ARognes/Gravi/V0.1/Choc/main.kicad_sch

## KiCad design V0.1/Choc/main.kicad_sch (2022-05-29, an earlier design)

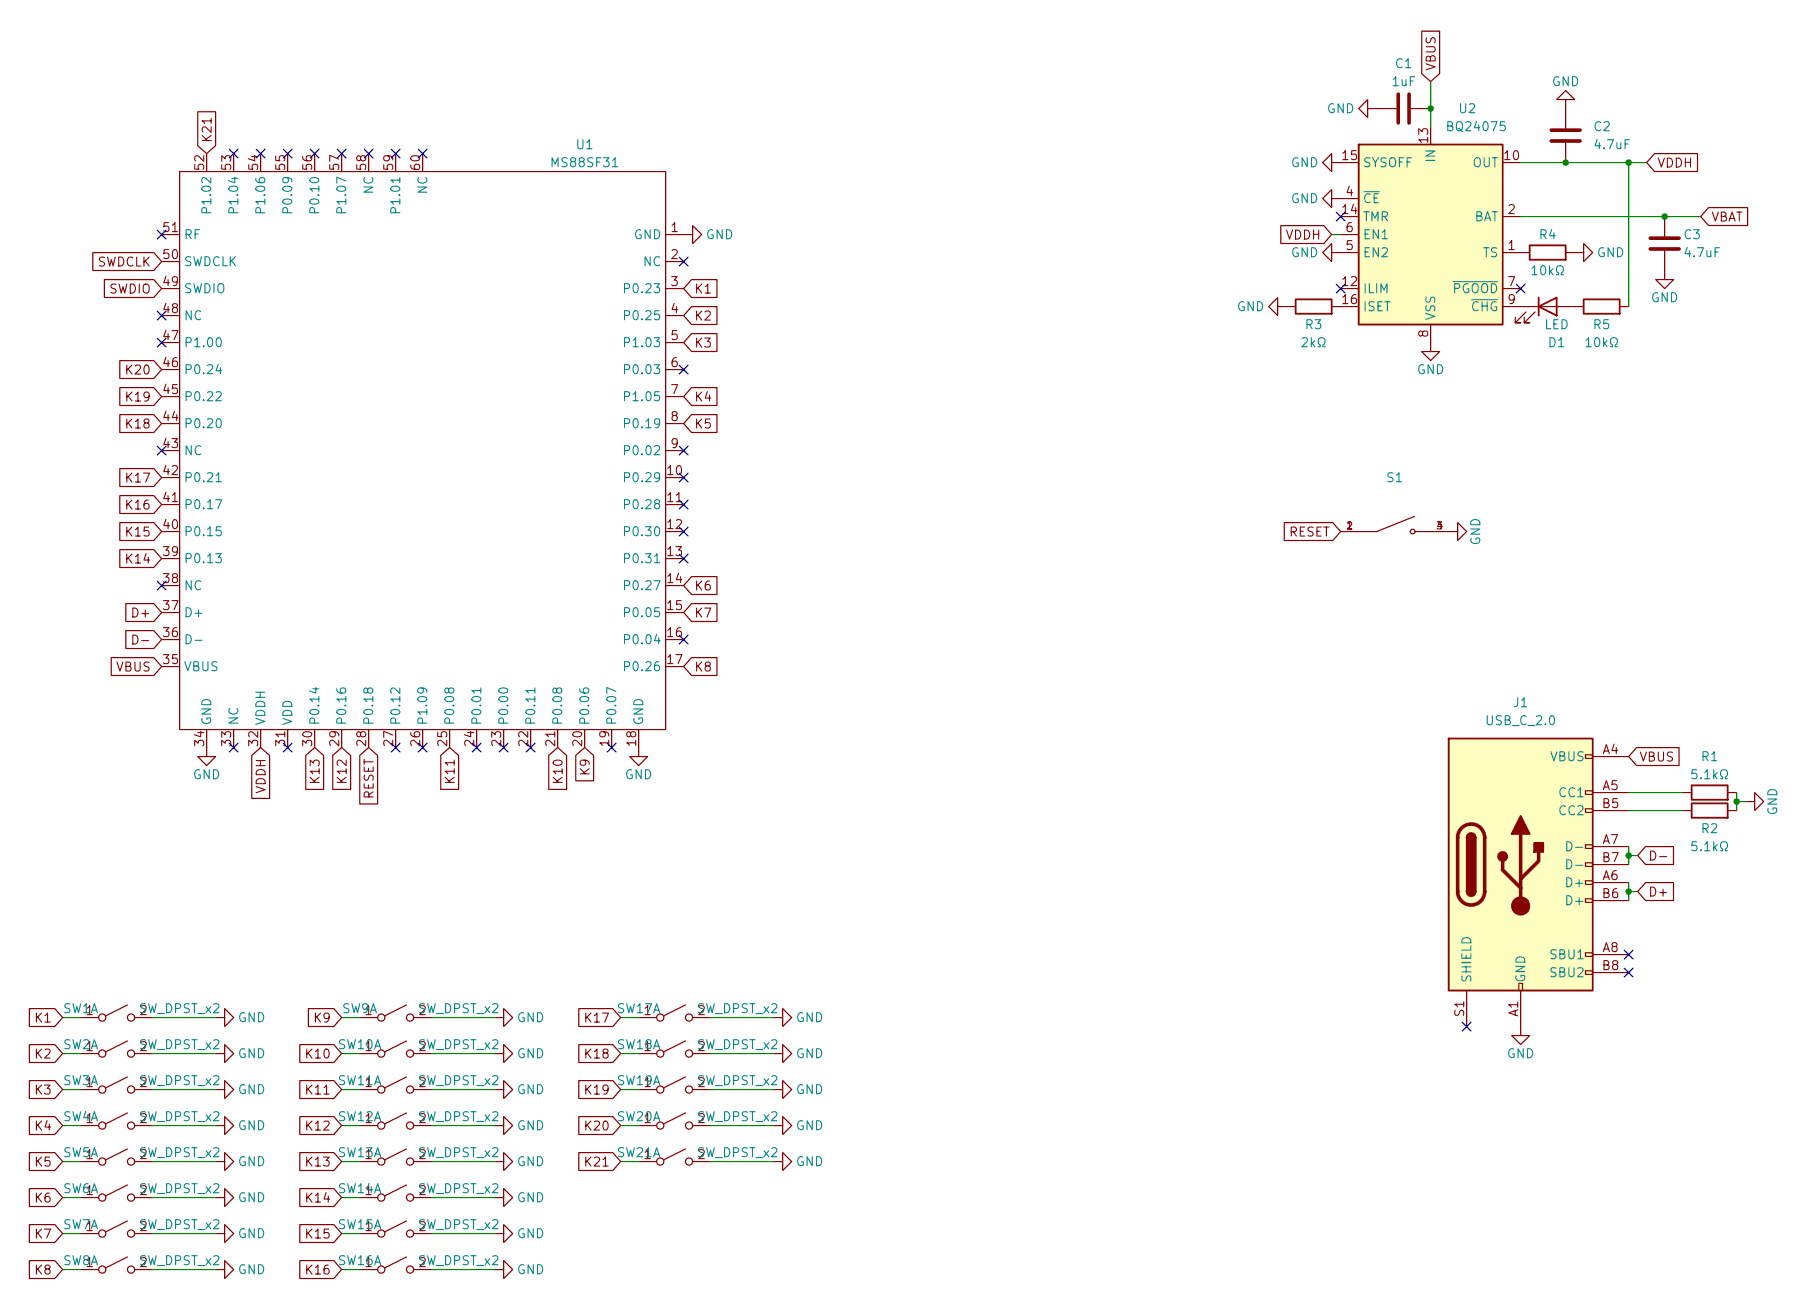
[picture p16: schematic main.kicad_sch]

Parts:
C1: 1uF
C2, C3: 4.7uF
D1: LED
J1: USB_C_2.0
R1, R2: 5.1kΩ
R3: 2kΩ
R4, R5: 10kΩ
S1: PARTREV 20 mar 19
SW1, SW2, SW3, SW4, SW5, SW6, SW7, SW8, SW9, SW10, SW11, SW12, SW13, SW14, SW15, SW16, SW17, SW18, SW19, SW20, SW21: SW_DPST_x2
U1: MS88SF31; MS88SF3
U2: BQ24075; VQFN-16-1EP_3x3mm_P0.5mm_EP1.6x1.6mm

Connections:
D+: J1.A6 (D+), J1.B6 (D+), U1.37 (D+)
D-: J1.A7 (D-), J1.B7 (D-), U1.36 (D-)
GND: C1.1, C2.2, C3.1, J1.A1 (GND), J1.A12 (GND), J1.B1 (GND), J1.B12 (GND), R1.2, R2.2, R3.1, R4.2, SW1.2 (B), SW2.2 (B), SW3.2 (B), SW4.2 (B), SW5.2 (B), SW6.2 (B), SW7.2 (B), SW8.2 (B), SW9.2 (B), SW10.2 (B), SW11.2 (B), SW12.2 (B), SW13.2 (B), SW14.2 (B), SW15.2 (B), SW16.2 (B), SW17.2 (B), SW18.2 (B), SW19.2 (B), SW20.2 (B), SW21.2 (B), U1.1 (GND), U1.18 (GND), U1.34 (GND), U2.4 (~CE), U2.5 (EN2), U2.8 (VSS), U2.15 (SYSOFF), U2.17 (VSS)
K1: SW1.1 (A), U1.3 (P0.23)
K2: SW2.1 (A), U1.4 (P0.25)
K3: SW3.1 (A), U1.5 (P1.03)
K4: SW4.1 (A), U1.7 (P1.05)
K5: SW5.1 (A), U1.8 (P0.19)
K6: SW6.1 (A), U1.14 (P0.27)
K7: SW7.1 (A), U1.15 (P0.05)
K8: SW8.1 (A), U1.17 (P0.26)
K9: SW9.1 (A), U1.20 (P0.06)
K10: SW10.1 (A), U1.21 (P0.08)
K11: SW11.1 (A), U1.25 (P0.08)
K12: SW12.1 (A), U1.29 (P0.16)
K13: SW13.1 (A), U1.30 (P0.14)
K14: SW14.1 (A), U1.39 (P0.13)
K15: SW15.1 (A), U1.40 (P0.15)
K16: SW16.1 (A), U1.41 (P0.17)
K17: SW17.1 (A), U1.42 (P0.21)
K18: SW18.1 (A), U1.44 (P0.20)
K19: SW19.1 (A), U1.45 (P0.22)
K20: SW20.1 (A), U1.46 (P0.24)
K21: SW21.1 (A), U1.52 (P1.02)
unnamed: D1.1 (K), U2.9 (~CHG)
unnamed: D1.2 (A), R5.1
unnamed: J1.A5 (CC1), R1.1
unnamed: J1.B5 (CC2), R2.1
unnamed: R3.2, U2.16 (ISET)
unnamed: R4.1, U2.1 (TS)
unnamed: S1.3, S1.4
RESET: S1.1, S1.2, U1.28 (P0.18)
SWDCLK: U1.50 (SWDCLK)
SWDIO: U1.49 (SWDIO)
VBAT: C3.2, U2.2 (BAT), U2.3 (BAT)
VBUS: C1.2, J1.A4 (VBUS), J1.A9 (VBUS), J1.B4 (VBUS), J1.B9 (VBUS), U1.35 (VBUS), U2.13 (IN)
VDDH: C2.1, R5.2, U1.32 (VDDH), U2.6 (EN1), U2.10 (OUT), U2.11 (OUT)
