ARognes/Gravi/V0.2/Choc/main.kicad_sch

## KiCad design V0.2/Choc/main.kicad_sch (2022-08-15, an earlier design)

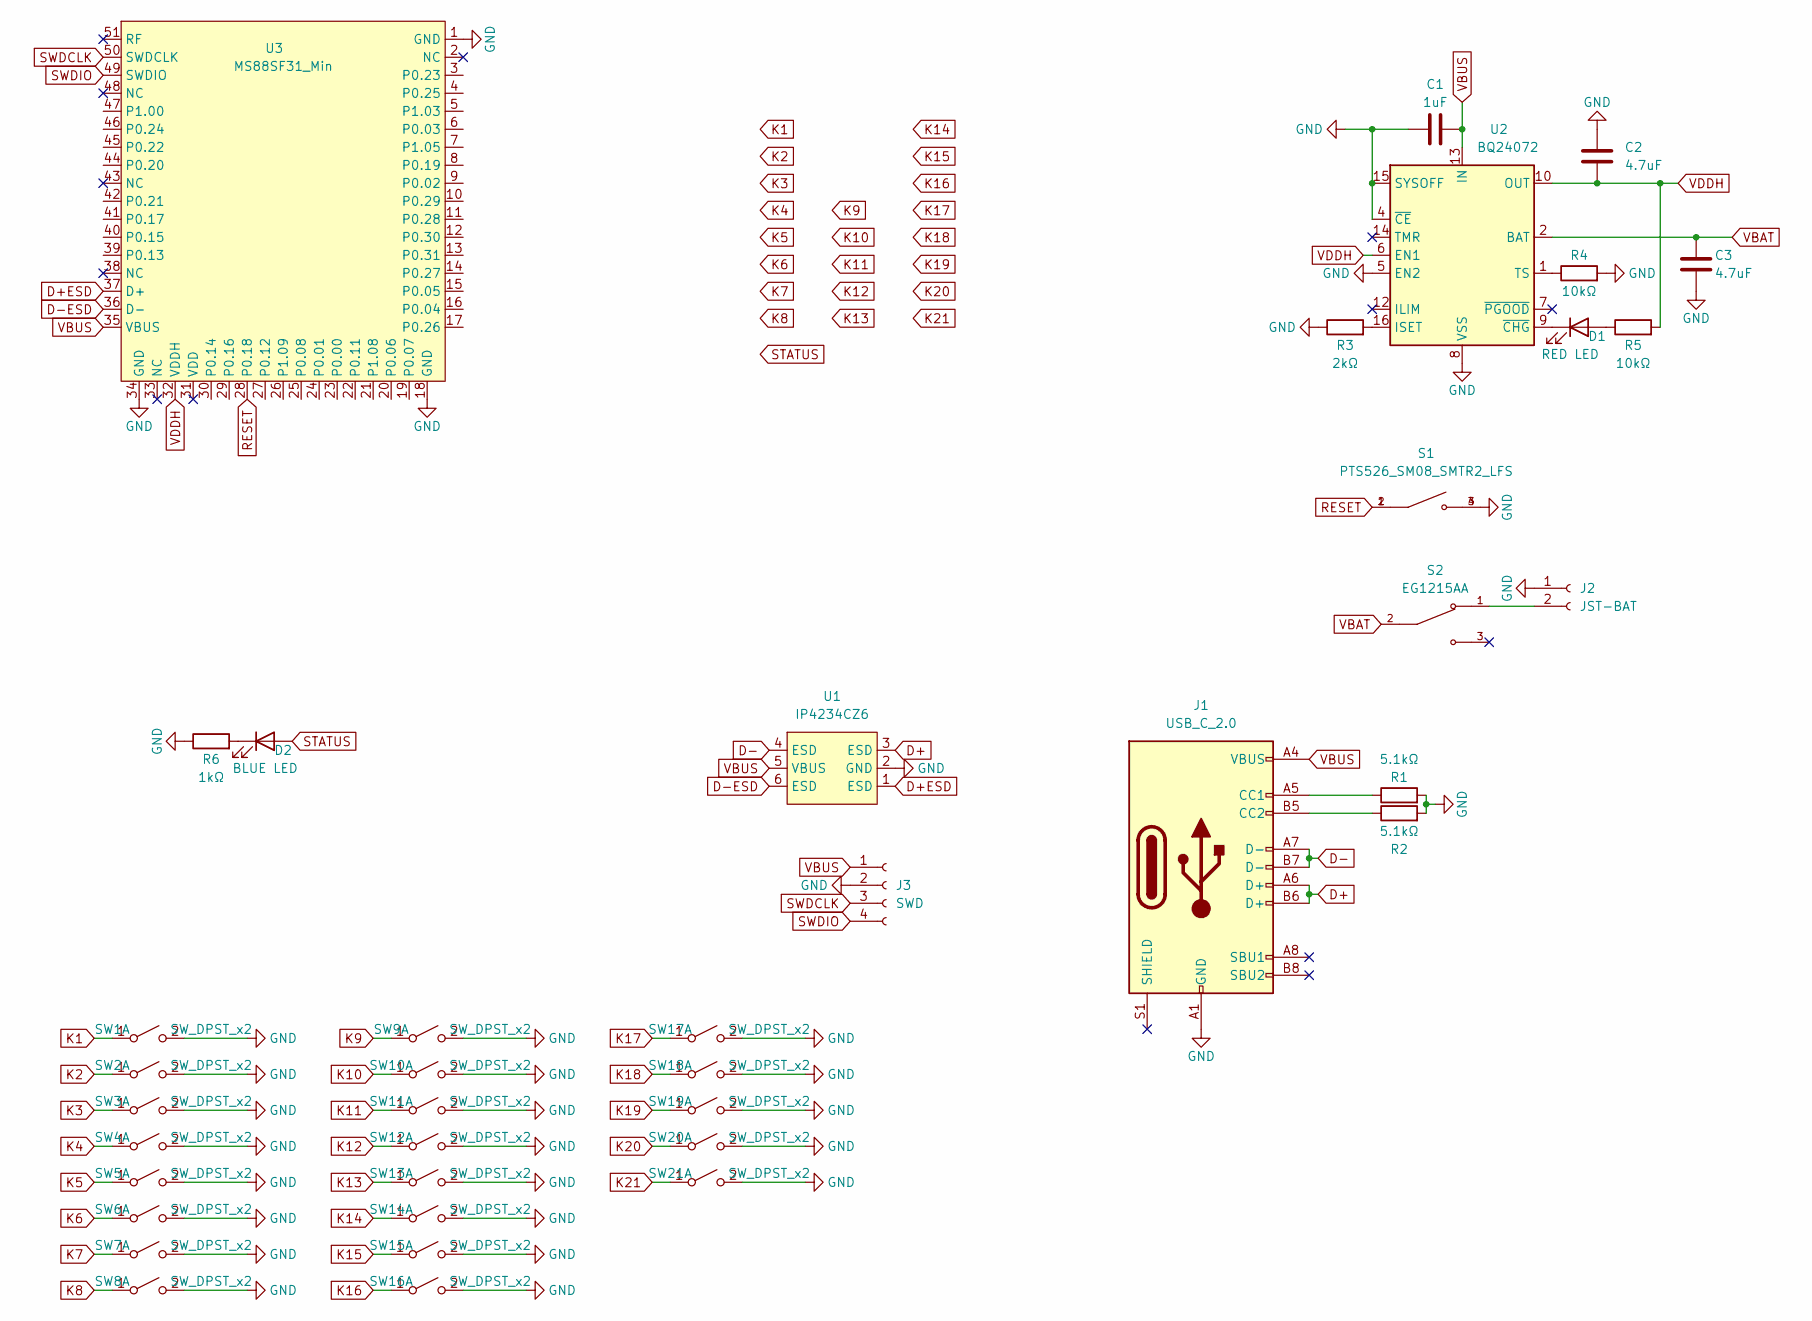
[picture p17: schematic main.kicad_sch]

Parts:
C1: 1uF
C2, C3: 4.7uF
D1: RED LED
D2: BLUE LED
J1: USB_C_2.0
J2: JST-BAT
J3: SWD
R1, R2: 5.1kΩ
R3: 2kΩ
R4, R5: 10kΩ
R6: 1kΩ
S1: PTS526_SM08_SMTR2_LFS; SW_PTS526_SM08_SMTR2_LFS; PARTREV 20 mar 19
S2: EG1215AA; SW_EG1215AA; PARTREV A
SW1, SW2, SW3, SW4, SW5, SW6, SW7, SW8, SW9, SW10, SW11, SW12, SW13, SW14, SW15, SW16, SW17, SW18, SW19, SW20, SW21: SW_DPST_x2
U1: IP4234CZ6
U2: BQ24072; VQFN-16-1EP_3x3mm_P0.5mm_EP1.6x1.6mm
U3: MS88SF31_Min

Connections:
D+: J1.A6 (D+), J1.B6 (D+), U1.3 (ESD)
D+ESD: U1.1 (ESD), U3.37 (D+)
D-: J1.A7 (D-), J1.B7 (D-), U1.4 (ESD)
D-ESD: U1.6 (ESD), U3.36 (D-)
GND: C1.1, C2.2, C3.1, J1.A1 (GND), J1.A12 (GND), J1.B1 (GND), J1.B12 (GND), J2.1, J3.2, R1.2, R2.2, R3.1, R4.2, R6.1, S1.3, S1.4, SW1.2 (B), SW2.2 (B), SW3.2 (B), SW4.2 (B), SW5.2 (B), SW6.2 (B), SW7.2 (B), SW8.2 (B), SW9.2 (B), SW10.2 (B), SW11.2 (B), SW12.2 (B), SW13.2 (B), SW14.2 (B), SW15.2 (B), SW16.2 (B), SW17.2 (B), SW18.2 (B), SW19.2 (B), SW20.2 (B), SW21.2 (B), U2.4 (~CE), U2.5 (EN2), U2.8 (VSS), U2.15 (SYSOFF), U2.17 (VSS), U3.18 (GND), U3.34 (GND)
K1: SW1.1 (A)
K2: SW2.1 (A)
K3: SW3.1 (A)
K4: SW4.1 (A)
K5: SW5.1 (A)
K6: SW6.1 (A)
K7: SW7.1 (A)
K8: SW8.1 (A)
K9: SW9.1 (A)
K10: SW10.1 (A)
K11: SW11.1 (A)
K12: SW12.1 (A)
K13: SW13.1 (A)
K14: SW14.1 (A)
K15: SW15.1 (A)
K16: SW16.1 (A)
K17: SW17.1 (A)
K18: SW18.1 (A)
K19: SW19.1 (A)
K20: SW20.1 (A)
K21: SW21.1 (A)
unnamed: D1.1 (K), U2.9 (~CHG)
unnamed: D1.2 (A), R5.1
unnamed: D2.1 (K), R6.2
unnamed: J1.A5 (CC1), R1.1
unnamed: J1.B5 (CC2), R2.1
unnamed: J2.2, S2.1
unnamed: R3.2, U2.16 (ISET)
unnamed: R4.1, U2.1 (TS)
RESET: S1.1, S1.2, U3.28 (P0.18)
STATUS: D2.2 (A)
SWDCLK: J3.3, U3.50 (SWDCLK)
SWDIO: J3.4, U3.49 (SWDIO)
VBAT: C3.2, S2.2, U2.2 (BAT), U2.3 (BAT)
VBUS: C1.2, J1.A4 (VBUS), J1.A9 (VBUS), J1.B4 (VBUS), J1.B9 (VBUS), J3.1, U1.5 (VBUS), U2.13 (IN), U3.35 (VBUS)
VDDH: C2.1, R5.2, U2.6 (EN1), U2.10 (OUT), U2.11 (OUT), U3.32 (VDDH)
