ARognes/Gravi/V0.4/Choc/main.kicad_sch

## KiCad design V0.4/Choc/main.kicad_sch (2023-01-30)

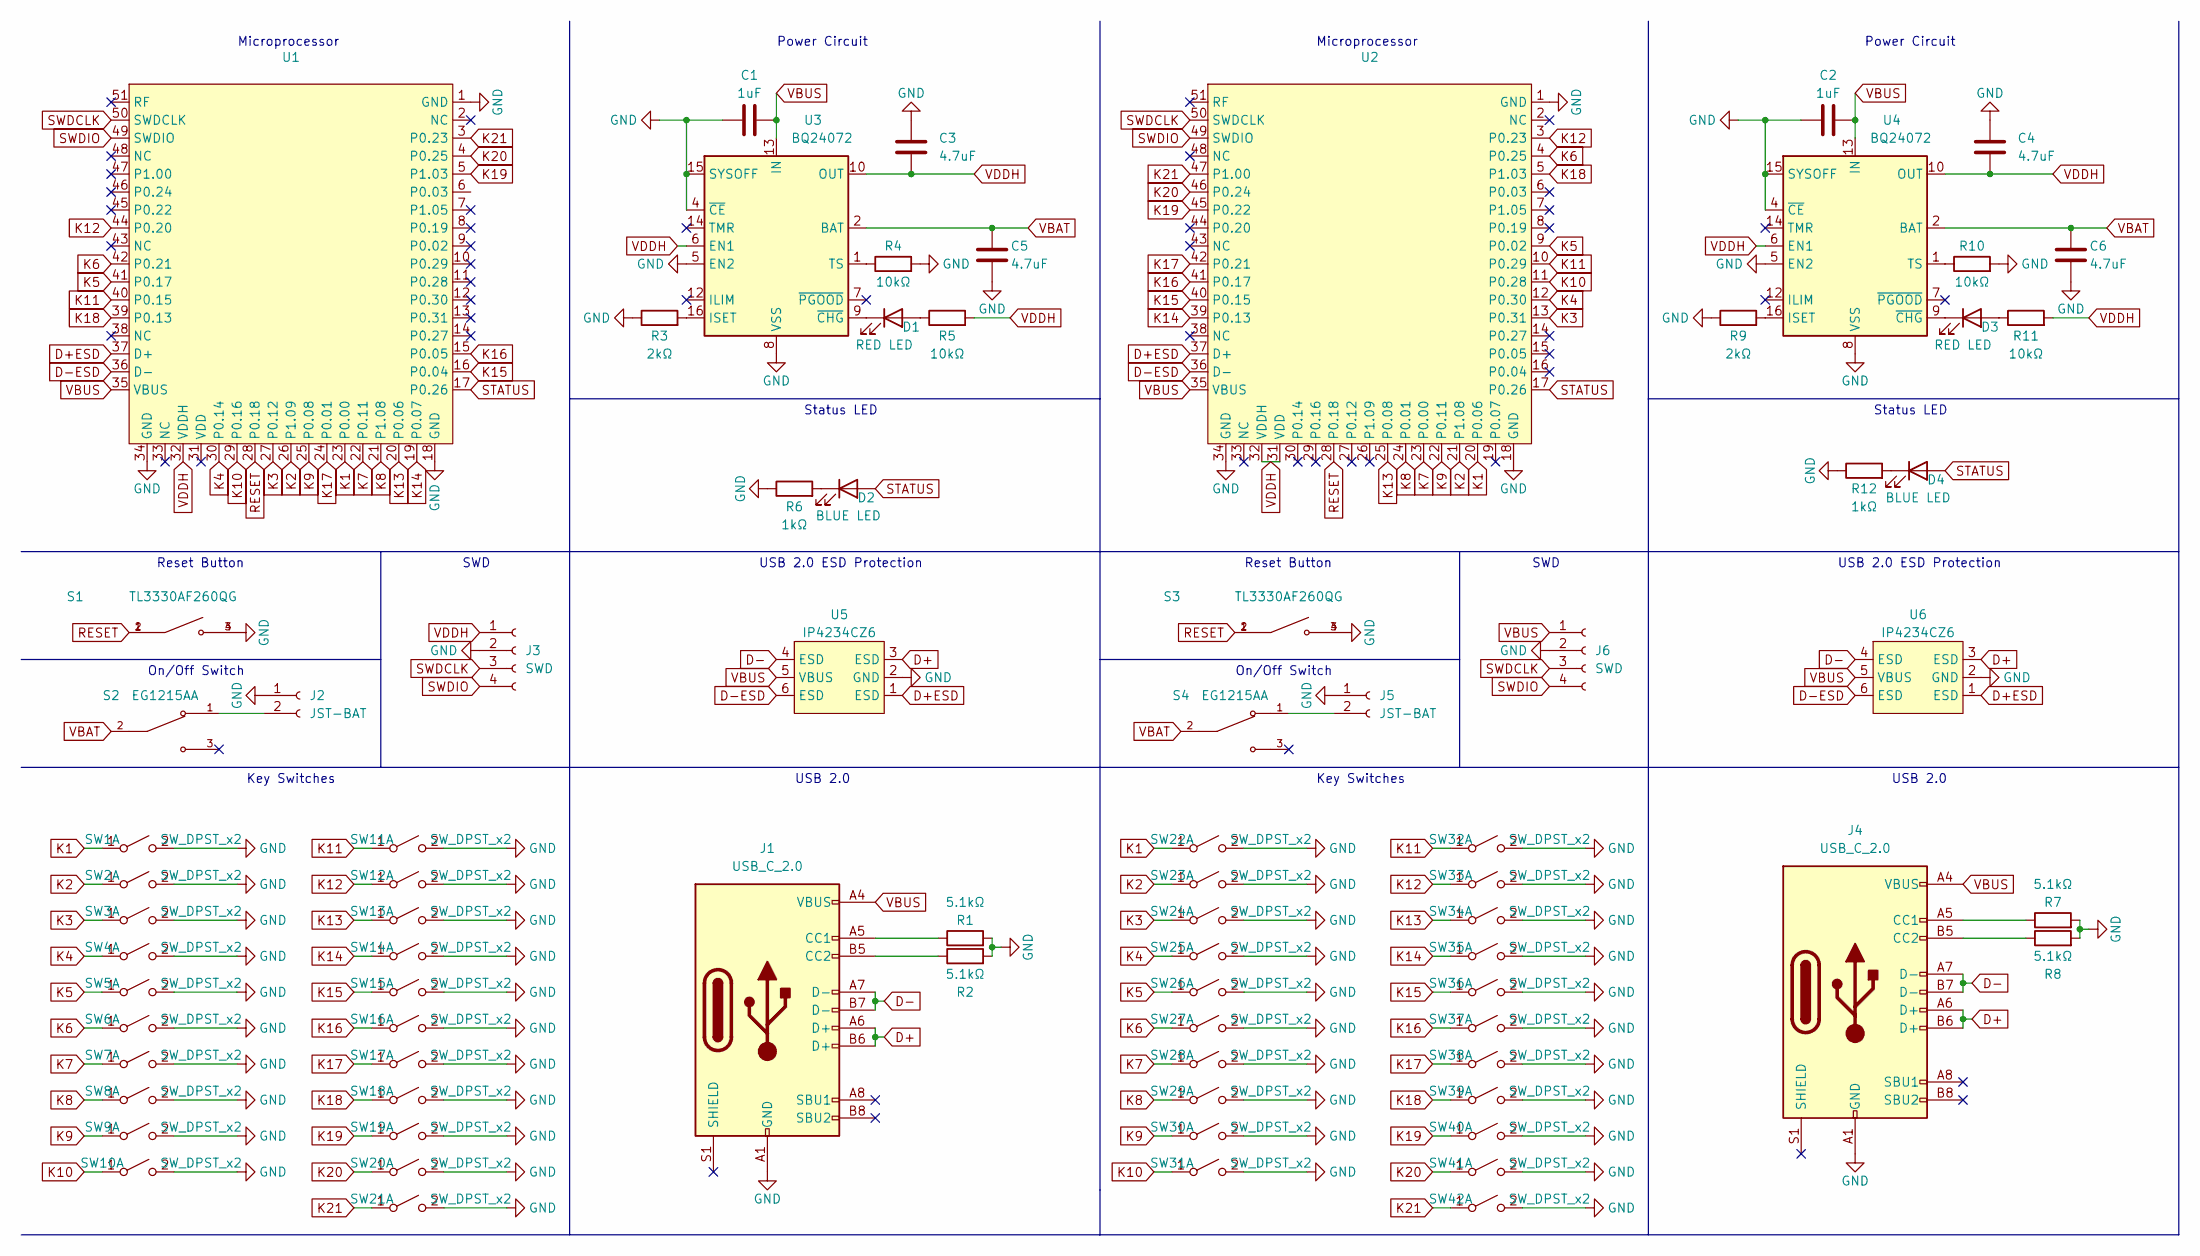
[picture p19: schematic main.kicad_sch]

Parts:
C1, C2: 1uF
C3, C4, C5, C6: 4.7uF
D1, D3: RED LED
D2, D4: BLUE LED
J1, J4: USB_C_2.0
J2, J5: JST-BAT
J3, J6: SWD
R1, R2, R7, R8: 5.1kΩ
R3, R9: 2kΩ
R4, R5, R10, R11: 10kΩ
R6, R12: 1kΩ
S1, S3: TL3330AF260QG; SW_PTS526_SM08_SMTR2_LFS; PARTREV 20 mar 19
S2, S4: EG1215AA; SW_EG1215AA; PARTREV A
SW1, SW2, SW3, SW4, SW5, SW6, SW7, SW8, SW9, SW10, SW11, SW12, SW13, SW14, SW15, SW16, SW17, SW18, SW19, SW20, SW21, SW22, SW23, SW24, SW25, SW26, SW27, SW28, SW29, SW30, SW31, SW32, SW33, SW34, SW35, SW36, SW37, SW38, SW39, SW40, SW41, SW42: SW_DPST_x2
U1, U2: (no value)
U3, U4: BQ24072; VQFN-16-1EP_3x3mm_P0.5mm_EP1.6x1.6mm
U5, U6: IP4234CZ6

Connections:
D+: J1.A6 (D+), J1.B6 (D+), J4.A6 (D+), J4.B6 (D+), U5.3 (ESD), U6.3 (ESD)
D+ESD: U1.37 (D+), U2.37 (D+), U5.1 (ESD), U6.1 (ESD)
D-: J1.A7 (D-), J1.B7 (D-), J4.A7 (D-), J4.B7 (D-), U5.4 (ESD), U6.4 (ESD)
D-ESD: U1.36 (D-), U2.36 (D-), U5.6 (ESD), U6.6 (ESD)
GND: C1.1, C2.1, C3.2, C4.2, C5.1, C6.1, J1.A1 (GND), J1.A12 (GND), J1.B1 (GND), J1.B12 (GND), J2.1, J3.2, J4.A1 (GND), J4.A12 (GND), J4.B1 (GND), J4.B12 (GND), J5.1, J6.2, R1.2, R2.2, R3.1, R4.2, R6.1, R7.2, R8.2, R9.1, R10.2, R12.1, S1.3, S1.4, S3.3, S3.4, SW1.2 (B), SW2.2 (B), SW3.2 (B), SW4.2 (B), SW5.2 (B), SW6.2 (B), SW7.2 (B), SW8.2 (B), SW9.2 (B), SW10.2 (B), SW11.2 (B), SW12.2 (B), SW13.2 (B), SW14.2 (B), SW15.2 (B), SW16.2 (B), SW17.2 (B), SW18.2 (B), SW19.2 (B), SW20.2 (B), SW21.2 (B), SW22.2 (B), SW23.2 (B), SW24.2 (B), SW25.2 (B), SW26.2 (B), SW27.2 (B), SW28.2 (B), SW29.2 (B), SW30.2 (B), SW31.2 (B), SW32.2 (B), SW33.2 (B), SW34.2 (B), SW35.2 (B), SW36.2 (B), SW37.2 (B), SW38.2 (B), SW39.2 (B), SW40.2 (B), SW41.2 (B), SW42.2 (B), U1.1 (GND), U1.18 (GND), U1.34 (GND), U2.1 (GND), U2.18 (GND), U2.34 (GND), U3.4 (~CE), U3.5 (EN2), U3.8 (VSS), U3.15 (SYSOFF), U3.17 (VSS), U4.4 (~CE), U4.5 (EN2), U4.8 (VSS), U4.15 (SYSOFF), U4.17 (VSS), U5.2 (GND), U6.2 (GND)
K1: SW1.1 (A), SW22.1 (A), U1.23 (P0.00), U2.20 (P0.06)
K2: SW2.1 (A), SW23.1 (A), U1.26 (P1.09), U2.21 (P1.08)
K3: SW3.1 (A), SW24.1 (A), U1.27 (P0.12), U2.13 (P0.31)
K4: SW4.1 (A), SW25.1 (A), U1.30 (P0.14), U2.12 (P0.30)
K5: SW5.1 (A), SW26.1 (A), U1.41 (P0.17), U2.9 (P0.02)
K6: SW6.1 (A), SW27.1 (A), U1.42 (P0.21), U2.4 (P0.25)
K7: SW7.1 (A), SW28.1 (A), U1.22 (P0.11), U2.23 (P0.00)
K8: SW8.1 (A), SW29.1 (A), U1.21 (P1.08), U2.24 (P0.01)
K9: SW9.1 (A), SW30.1 (A), U1.25 (P0.08), U2.22 (P0.11)
K10: SW10.1 (A), SW31.1 (A), U1.29 (P0.16), U2.11 (P0.28)
K11: SW11.1 (A), SW32.1 (A), U1.40 (P0.15), U2.10 (P0.29)
K12: SW12.1 (A), SW33.1 (A), U1.44 (P0.20), U2.3 (P0.23)
K13: SW13.1 (A), SW34.1 (A), U1.20 (P0.06), U2.25 (P0.08)
K14: SW14.1 (A), SW35.1 (A), U1.19 (P0.07), U2.39 (P0.13)
K15: SW15.1 (A), SW36.1 (A), U1.16 (P0.04), U2.40 (P0.15)
K16: SW16.1 (A), SW37.1 (A), U1.15 (P0.05), U2.41 (P0.17)
K17: SW17.1 (A), SW38.1 (A), U1.24 (P0.01), U2.42 (P0.21)
K18: SW18.1 (A), SW39.1 (A), U1.39 (P0.13), U2.5 (P1.03)
K19: SW19.1 (A), SW40.1 (A), U1.5 (P1.03), U2.45 (P0.22)
K20: SW20.1 (A), SW41.1 (A), U1.4 (P0.25), U2.46 (P0.24)
K21: SW21.1 (A), SW42.1 (A), U1.3 (P0.23), U2.47 (P1.00)
unnamed: D1.1 (K), U3.9 (~CHG)
unnamed: D1.2 (A), R5.1
unnamed: D2.1 (K), R6.2
unnamed: D3.1 (K), U4.9 (~CHG)
unnamed: D3.2 (A), R11.1
unnamed: D4.1 (K), R12.2
unnamed: J1.A5 (CC1), R1.1
unnamed: J1.B5 (CC2), R2.1
unnamed: J2.2, S2.1
unnamed: J4.A5 (CC1), R7.1
unnamed: J4.B5 (CC2), R8.1
unnamed: J5.2, S4.1
unnamed: R3.2, U3.16 (ISET)
unnamed: R4.1, U3.1 (TS)
unnamed: R9.2, U4.16 (ISET)
unnamed: R10.1, U4.1 (TS)
RESET: S1.1, S1.2, S3.1, S3.2, U1.28 (P0.18), U2.28 (P0.18)
STATUS: D2.2 (A), D4.2 (A), U1.17 (P0.26), U2.17 (P0.26)
SWDCLK: J3.3, J6.3, U1.50 (SWDCLK), U2.50 (SWDCLK)
SWDIO: J3.4, J6.4, U1.49 (SWDIO), U2.49 (SWDIO)
VBAT: C5.2, C6.2, S2.2, S4.2, U3.2 (BAT), U3.3 (BAT), U4.2 (BAT), U4.3 (BAT)
VBUS: C1.2, C2.2, J1.A4 (VBUS), J1.A9 (VBUS), J1.B4 (VBUS), J1.B9 (VBUS), J4.A4 (VBUS), J4.A9 (VBUS), J4.B4 (VBUS), J4.B9 (VBUS), J6.1, U1.35 (VBUS), U2.35 (VBUS), U3.13 (IN), U4.13 (IN), U5.5 (VBUS), U6.5 (VBUS)
VDDH: C3.1, C4.1, J3.1, R5.2, R11.2, U1.32 (VDDH), U2.31 (VDD), U2.32 (VDDH), U3.6 (EN1), U3.10 (OUT), U3.11 (OUT), U4.6 (EN1), U4.10 (OUT), U4.11 (OUT)

Notes on the sheet:
SWD
USB 2.0
Power Circuit
Key Switches
USB 2.0 ESD Protection
Status LED
Microprocessor
Reset Button
On/Off Switch
